kaiiorg/piHATlabs/images/1/3.1.jpg

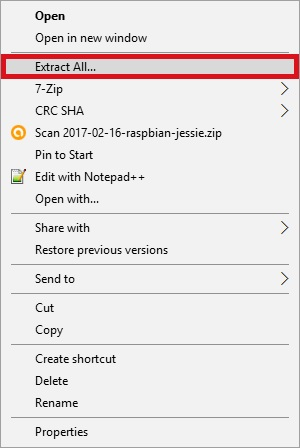
images/1/3.1.jpg
