kaiiorg/piHATlabs/images/1/3.2.jpg

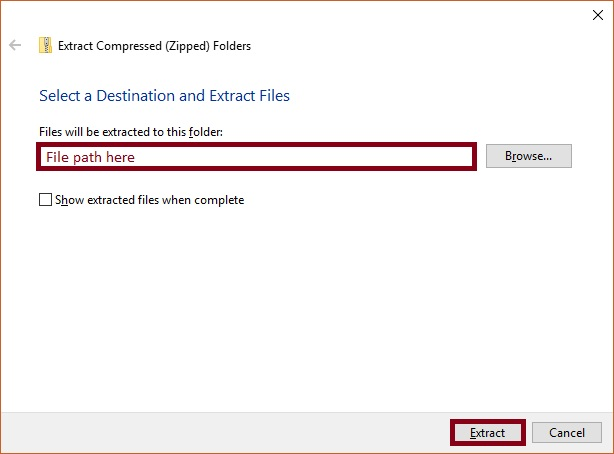
images/1/3.2.jpg
