kaiiorg/piHATlabs/images/1/6.3.jpg

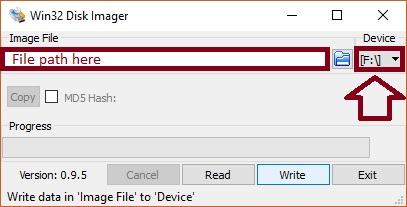
images/1/6.3.jpg
