kaiiorg/piHATlabs/images/1/6.4.jpg

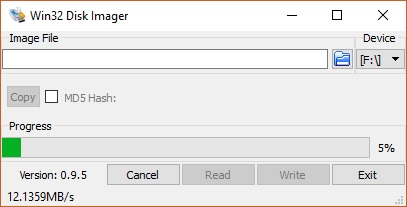
images/1/6.4.jpg
