kaiiorg/piHATlabs/images/1/7.6b.jpg

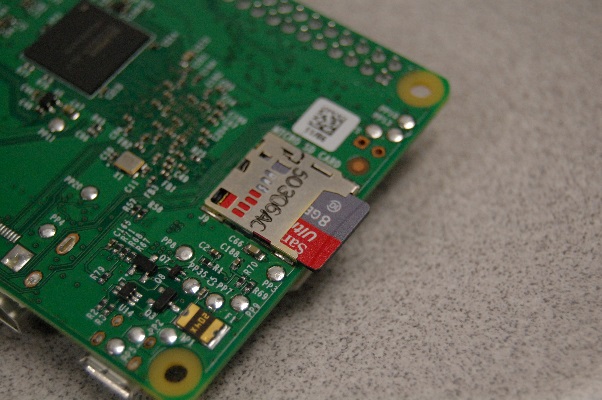
images/1/7.6b.jpg
