kaiiorg/piHATlabs/images/2/1.jpg

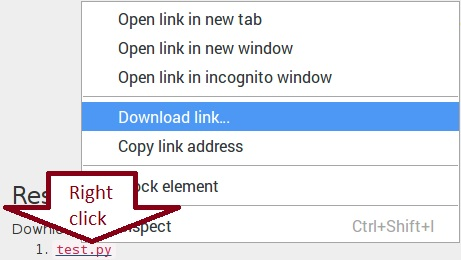
images/2/1.jpg
