kaiiorg/piHATlabs/images/2/3.jpg

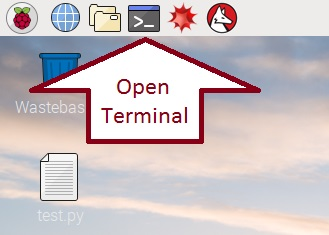
images/2/3.jpg
