kaiiorg/piHATlabs/images/2/5.jpg

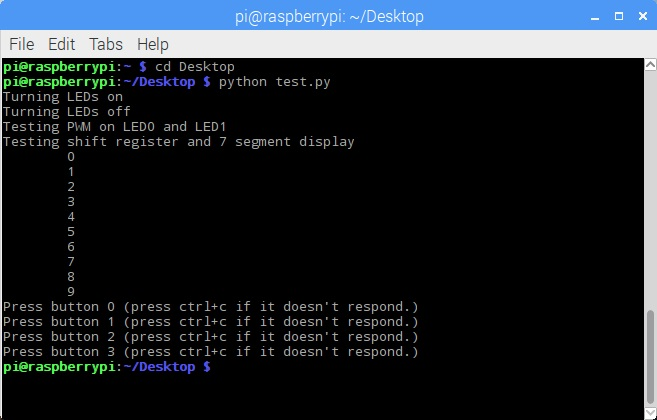
images/2/5.jpg
