kaiiorg/piHATlabs/images/2/layout.1.jpg

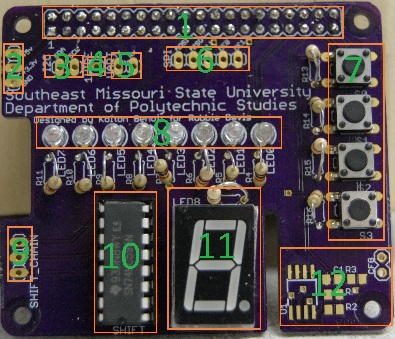
images/2/layout.1.jpg
