kaiiorg/piHATlabs/images/3/7.1.png

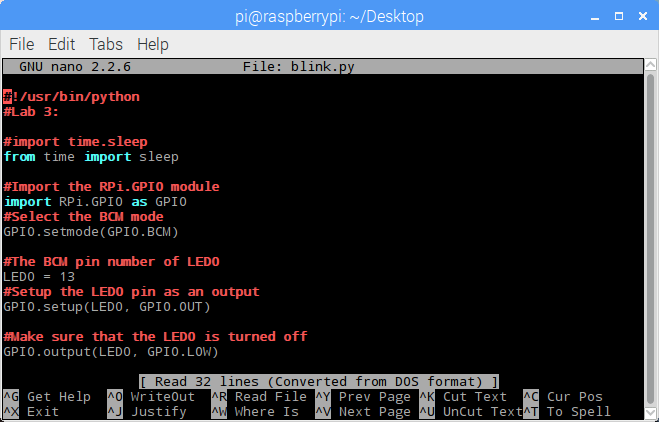
images/3/7.1.png
