kaiiorg/piHATlabs/images/3/layout.2.jpg

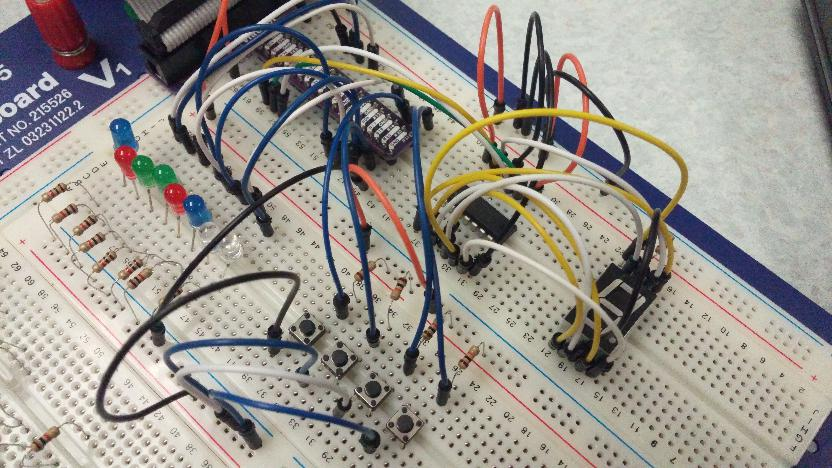
images/3/layout.2.jpg
