kaiiorg/piHATlabs/images/3/sch.6.png

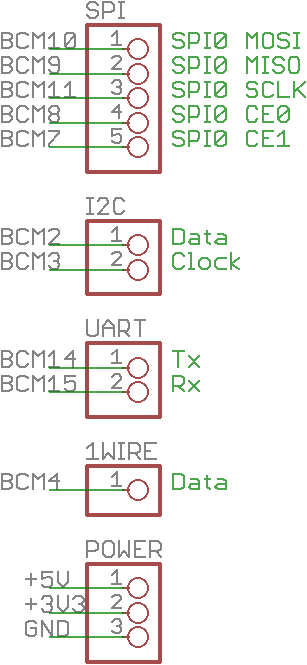
images/3/sch.6.png
