kaiiorg/piHATlabs/images/3/sch.7.png

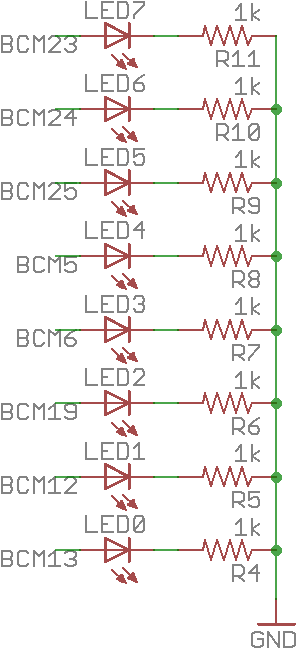
images/3/sch.7.png
