kaiiorg/piHATlabs/images/3/sch.8.png

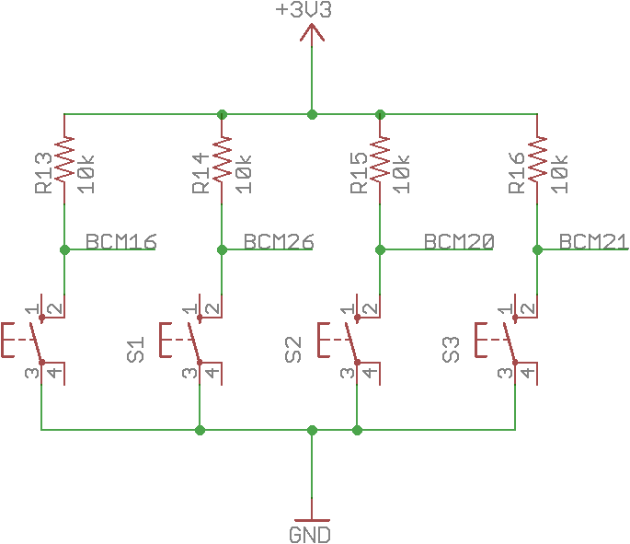
images/3/sch.8.png
