kaiiorg/piHATlabs/images/3/sch.10.png

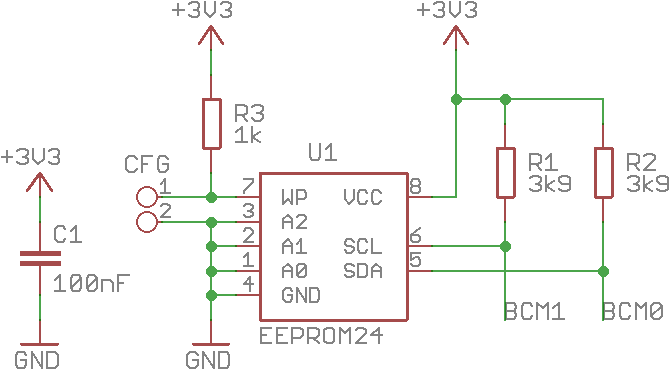
images/3/sch.10.png
