kaiiorg/piHATlabs/images/3/v1.1.png

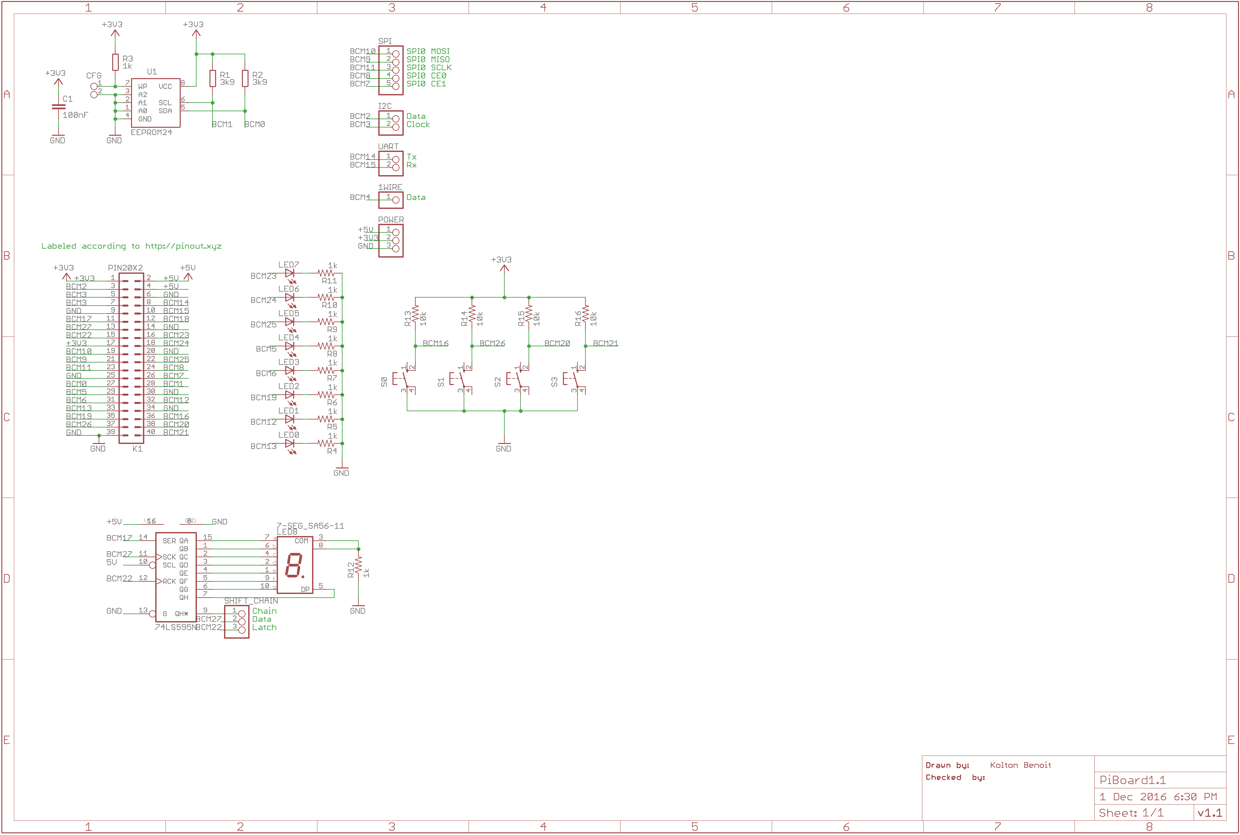
images/3/v1.1.png
