kaiiorg/piHATlabs/images/4/sch.1.png

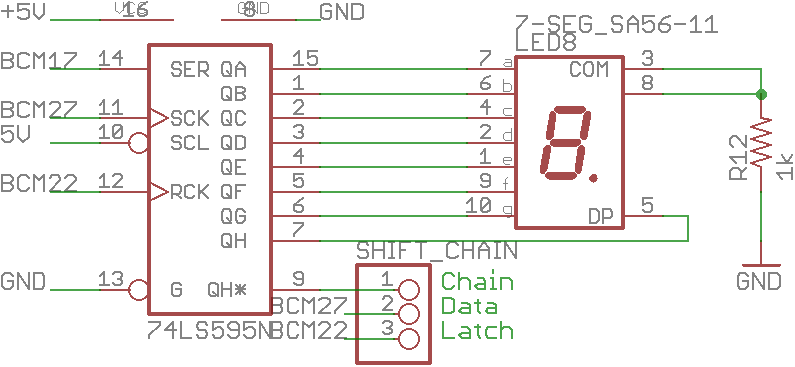
images/4/sch.1.png
