kaiiorg/piHATlabs/images/4/sch.2.png

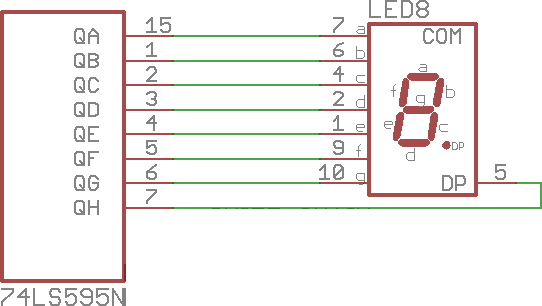
images/4/sch.2.png
