kaiiorg/piHATlabs/images/hatPrototype.jpg

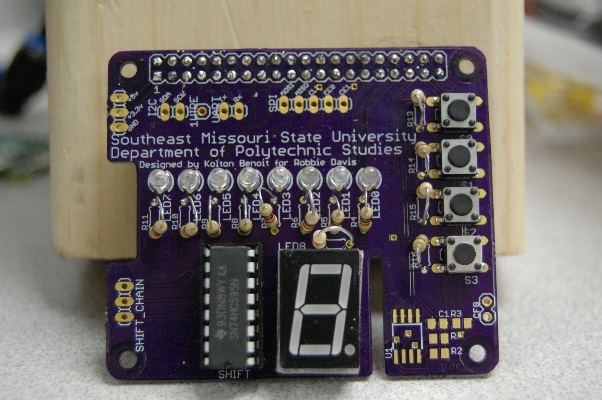
images/hatPrototype.jpg
